pieeg-club/BioRon_EEG/supplementary files/image_2.jpg

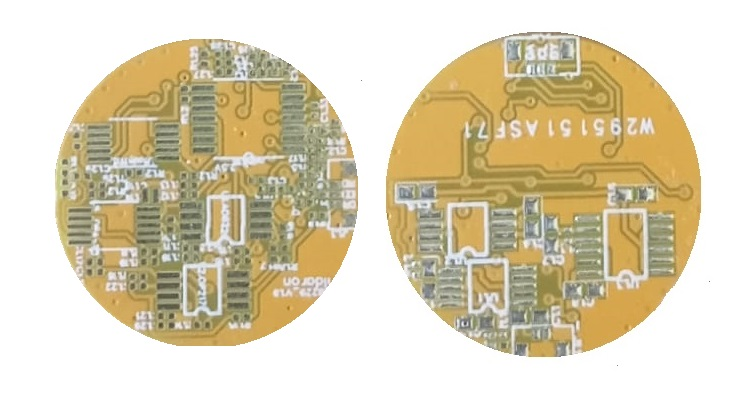
supplementary files/image_2.jpg
